michael-betz/espirgbani_pio/src/wifi.c

#include "json_settings.h"
#include "lwip/apps/sntp.h"
#include "lwip/sockets.h"
#include <string.h>
// #include "lwip/sys.h"
#include "esp_event.h"
#include "esp_log.h"
#include "esp_wifi.h"
#include "lwip/dns.h"
#include "lwip/netdb.h"
#include "mdns.h"
#include "nvs_flash.h"
#include "rom/rtc.h"
#include "static_ws.h"
#include "wifi.h"

#include "esp_dpp.h"
#include "qrcode.h"

#define E(x) ESP_ERROR_CHECK_WITHOUT_ABORT(x)

static const char *T = "WIFI";

t_wifi_state wifi_state = WIFI_NOT_CONNECTED;
esp_ip4_addr_t wifi_ip = {0};
char wifi_ssid[32] = {0};

// -----------------------------------------------
//  Websocket logger
// -----------------------------------------------
// Rolling buffer size in RTC mem for log entries in bytes
#define LOG_FILE_SIZE 3576

// put the buffer and write pointer in RTC memory,
// such that it survives sleep mode
RTC_NOINIT_ATTR static char rtcLogBuffer[LOG_FILE_SIZE];
RTC_NOINIT_ATTR static char *rtcLogWritePtr = rtcLogBuffer;
RTC_NOINIT_ATTR static char *rtcLogReadPtr = rtcLogBuffer;

static const char *logBuffEnd = rtcLogBuffer + LOG_FILE_SIZE - 1;

// The unmodified stdout file
FILE *old_stdout = NULL;
FILE *old_stderr = NULL;

// add stdout chars to the RTC log buffer.
static int print_to_ws(void *cookie, const char *data, int size) {
	if (old_stdout != NULL)
		fwrite(data, 1, size, old_stdout);

	// ring-buffer in RTC memory for persistence in sleep mode
	for (unsigned i = 0; i < size; i++) {
		char c = data[i];

		*rtcLogWritePtr = c;
		if (rtcLogWritePtr >= logBuffEnd) {
			rtcLogWritePtr = rtcLogBuffer;
		} else {
			rtcLogWritePtr++;
		}
	}

	return size;
}

void web_console_init() {
	static char linebuf[128];

	ESP_LOGI(T, "Enabling web-socket logging 👋");

	int reason = rtc_get_reset_reason(0);
	if (reason == POWERON_RESET) {
		ESP_LOGW(T, "Clearing RTC log");
		memset(rtcLogBuffer, 0, LOG_FILE_SIZE);
		rtcLogWritePtr = rtcLogBuffer;
		rtcLogReadPtr = rtcLogBuffer;
	} else {
		if (rtcLogWritePtr < rtcLogBuffer || rtcLogWritePtr > logBuffEnd)
			rtcLogWritePtr = rtcLogBuffer;

		if (rtcLogReadPtr < rtcLogBuffer || rtcLogReadPtr > logBuffEnd)
			rtcLogReadPtr = rtcLogBuffer;
	}

	// Keep a copy for printing to UART
	old_stdout = stdout;
	old_stderr = stderr;

	// standard IO streams are inherited when a task is created, so this needs
	// to be done before creating other tasks:
	_GLOBAL_REENT->_stdout = fwopen(NULL, &print_to_ws);
	_GLOBAL_REENT->_stderr = fwopen(NULL, &print_to_ws);

	// Also redirect stdout/stderr of main task
	stdout = _GLOBAL_REENT->_stdout;
	stderr = _GLOBAL_REENT->_stderr;

	setvbuf(stdout, linebuf, _IOLBF, sizeof(linebuf));
}

void wsDumpRtc(httpd_req_t *req, bool dump_all) {
	int n_bytes = 0;

	if (dump_all) {
		n_bytes = LOG_FILE_SIZE;
		rtcLogReadPtr = rtcLogWritePtr;
	} else {
		n_bytes = (rtcLogWritePtr - rtcLogReadPtr + LOG_FILE_SIZE);
		n_bytes %= LOG_FILE_SIZE;
	}

	if (n_bytes <= 0)
		return;

	char *buffer = malloc(n_bytes + 1);
	if (!buffer)
		return;

	char *p = buffer;
	*p++ = 'a';

	for (unsigned i = 0; i < n_bytes; i++) {
		*p++ = *rtcLogReadPtr++;
		if (rtcLogReadPtr > logBuffEnd)
			rtcLogReadPtr = rtcLogBuffer;
	}

	httpd_ws_frame_t wsf = {0};
	wsf.type = HTTPD_WS_TYPE_TEXT;
	wsf.payload = (uint8_t *)buffer;
	wsf.len = n_bytes + 1;
	httpd_ws_send_frame(req, &wsf);

	free(buffer);
}

// go through wifi scan results and look for the first known wifi
// if the wifi is known, meaning it is configured in the .json, connect to it
// if no known wifi is found, start the AP
static void scan_done(
	void *arg, esp_event_base_t event_base, int32_t event_id, void *event_data
) {
	uint16_t n = 24;
	static wifi_ap_record_t ap_info[24];

	E(esp_wifi_scan_get_ap_records(&n, ap_info));

	if (n < 1) {
		ESP_LOGE(T, "wifi scan failed");
		return;
	}

	cJSON *jWifi, *jWifis = jGet(getSettings(), "wifis");
	if (!jWifis) {
		ESP_LOGE(T, "no wifis defined in .json");
		return;
	}

	// Go through all found APs, use ssid as key and try to get item from json
	ESP_LOGI(T, "Wifis I can see:");
	for (unsigned i = 0; i < n; i++) {
		ESP_LOGI(
			T, "    %s (%d, %d dBm)", ap_info[i].ssid, ap_info[i].primary,
			ap_info[i].rssi
		);
	}

	for (unsigned i = 0; i < n; i++) {
		const char *ssid = (const char *)ap_info[i].ssid;
		jWifi = jGet(jWifis, ssid);
		if (!cJSON_IsString(jWifi))
			continue;

		// Found a known good WIFI, connect to it ...
		ESP_LOGI(T, "Looks familiar: %s", ssid);
		char *pw = jWifi->valuestring;
		wifi_config_t cfg;
		memset(&cfg, 0, sizeof(cfg));
		strncpy((char *)cfg.sta.ssid, ssid, 31);
		strncpy(wifi_ssid, ssid, sizeof(wifi_ssid));
		strncpy((char *)cfg.sta.password, pw, 63);
		cfg.sta.scan_method = WIFI_FAST_SCAN;
		cfg.sta.bssid_set = true;
		memcpy(cfg.sta.bssid, ap_info[i].bssid, 6);
		cfg.sta.channel = ap_info[i].primary;
		cfg.sta.pmf_cfg.capable = true;

		E(esp_wifi_set_mode(WIFI_MODE_STA));
		E(esp_wifi_set_config(ESP_IF_WIFI_STA, &cfg));
		E(esp_wifi_connect());
		E(esp_wifi_set_ps(WIFI_PS_MAX_MODEM));
		return;
	}

	ESP_LOGW(T, "no known Wifi found");
	wifi_state = WIFI_NOT_CONNECTED;
}

static void got_ip(
	void *arg, esp_event_base_t event_base, int32_t event_id, void *event_data
) {
	ip_event_got_ip_t *event = (ip_event_got_ip_t *)event_data;
	wifi_ip = event->ip_info.ip;
	ESP_LOGI(T, "Got ip " IPSTR, IP2STR(&event->ip_info.ip));

	// trigger time sync
	sntp_setoperatingmode(SNTP_OPMODE_POLL);
	const char *ntp_str = jGetS(getSettings(), "ntp_host", "pool.ntp.org");
	sntp_setservername(0, ntp_str);
	sntp_init();

	wifi_state = WIFI_CONNECTED;
}

static void got_discon(
	void *arg, esp_event_base_t event_base, int32_t event_id, void *event_data
) {
	ESP_LOGW(T, "got disconnected :(");
	if (event_data) {
		wifi_event_sta_disconnected_t *ed =
			(wifi_event_sta_disconnected_t *)event_data;
		ESP_LOGW(T, "reason: %d", ed->reason);
	}

	sntp_stop();
	wifi_state = WIFI_NOT_CONNECTED;
}

static void dpp_enrollee_event_cb(esp_supp_dpp_event_t event, void *data) {
	static int retries = 8;

	switch (event) {
	case ESP_SUPP_DPP_URI_READY:
		retries = 8;
		if (data != NULL) {
			esp_qrcode_config_t cfg = ESP_QRCODE_CONFIG_DEFAULT();
			ESP_LOGI(T, "Scan below QR Code to configure the enrollee:\n");
			esp_qrcode_generate(&cfg, (const char *)data);
		}
		break;

	case ESP_SUPP_DPP_CFG_RECVD:
		retries = 8;
		wifi_config_t s_dpp_wifi_config;
		memcpy(&s_dpp_wifi_config, data, sizeof(s_dpp_wifi_config));
		ESP_LOGI(
			T, "DPP Authentication successful, ssid: %s",
			s_dpp_wifi_config.sta.ssid
		);
		// TODO store ssid and pw in .json config, then call tryJsonConnect()
		break;

	case ESP_SUPP_DPP_FAIL:
		ESP_LOGW(T, "DPP Auth failed (Reason: %s)", esp_err_to_name((int)data));
		if (retries-- > 0) {
			ESP_LOGI(T, "retry ...");
			E(esp_supp_dpp_start_listen());
		}
		break;

	default:
		break;
	}
}

static wifi_config_t wifi_ap_config = {
	.ap =
		{
			.channel = 6,
			.max_connection = 3,
			.authmode = WIFI_AUTH_OPEN,
			.pmf_cfg =
				{
					.required = false,
				},
		},
};

void initWifi() {
	// Initialize NVS
	esp_err_t ret = nvs_flash_init();
	if (ret == ESP_ERR_NVS_NO_FREE_PAGES ||
		ret == ESP_ERR_NVS_NEW_VERSION_FOUND) {
		E(nvs_flash_erase());
		ret = nvs_flash_init();
	}
	E(ret);

	E(esp_netif_init());
	E(esp_event_loop_create_default());

	// register some async callbacks
	E(esp_event_handler_register(
		WIFI_EVENT, WIFI_EVENT_SCAN_DONE, &scan_done, NULL
	));
	E(esp_event_handler_register(IP_EVENT, IP_EVENT_STA_GOT_IP, &got_ip, NULL));
	E(esp_event_handler_register(
		WIFI_EVENT, WIFI_EVENT_STA_DISCONNECTED, &got_discon, NULL
	));
	E(esp_event_handler_register(
		WIFI_EVENT, WIFI_EVENT_STA_STOP, &got_discon, NULL
	));

	wifi_init_config_t cfg = WIFI_INIT_CONFIG_DEFAULT();
	E(esp_wifi_init(&cfg));

	// Initialize default station as network interface instance (esp-netif)
	esp_netif_t *sta_netif = esp_netif_create_default_wifi_sta();
	assert(sta_netif);
	esp_netif_t *ap_netif = esp_netif_create_default_wifi_ap();
	assert(ap_netif);

	// Init DNS and mDNS
	const char *hostname = jGetS(getSettings(), "hostname", "espirgbani");
	E(esp_netif_set_hostname(sta_netif, hostname));
	E(mdns_init());
	E(mdns_hostname_set(hostname));

	// Set the timezone
	const char *tz_str = jGetS(getSettings(), "timezone", "PST8PDT");
	ESP_LOGI(T, "Setting timezone to TZ = %s", tz_str);
	setenv("TZ", tz_str, 1);
	tzset();

	// Setup AP mode (may be used if no known wifi is found)
	int l = strlen(hostname);
	if (l > sizeof(wifi_ap_config.ap.ssid))
		l = sizeof(wifi_ap_config.ap.ssid);
	wifi_ap_config.ap.ssid_len = l;
	memcpy(wifi_ap_config.ap.ssid, hostname, l);

	E(esp_wifi_set_mode(WIFI_MODE_STA));
	E(esp_wifi_start());
}

void tryJsonConnect() {
	// Disable wifi if there are no entries in settings.json
	cJSON *jWifis = jGet(getSettings(), "wifis");
	if (!jWifis || cJSON_GetArraySize(jWifis) <= 0) {
		ESP_LOGW(T, "No wifis defined in .json. Disabling wifi.");
		wifi_state = WIFI_DISABLED;
		return;
	}

	// Initialize and start WiFi scan
	E(esp_wifi_set_mode(WIFI_MODE_STA));
	E(esp_wifi_scan_start(NULL, false));
	// fires SYSTEM_EVENT_SCAN_DONE when done, calls scan_done() ...
	wifi_state = WIFI_SCANNING;
}

void tryApMode() {
	E(esp_wifi_set_mode(WIFI_MODE_AP));
	E(esp_wifi_set_config(WIFI_IF_AP, &wifi_ap_config));
	ESP_LOGI(T, "started AP mode. SSID: %s", wifi_ap_config.ap.ssid);
	strncpy(wifi_ssid, (const char *)wifi_ap_config.ap.ssid, sizeof(wifi_ssid));
	wifi_state = WIFI_AP_MODE;
}

void tryEasyConnect() {
	// nice idea but doesn't work
	E(esp_wifi_set_mode(WIFI_MODE_STA));
	E(esp_supp_dpp_init(dpp_enrollee_event_cb));
	E(esp_supp_dpp_bootstrap_gen(
		"6", // DPP Bootstrapping listen channels separated by commas.
		DPP_BOOTSTRAP_QR_CODE,
		NULL, // Private key string for DPP Bootstrapping in PEM format.
		NULL  // Additional ancillary information to be included in QR Code.
	));

	E(esp_supp_dpp_start_listen());
	ESP_LOGI(T, "Started listening for DPP Authentication");
	wifi_state = WIFI_DPP_LISTENING;
}
