michael-betz/espirgbani_pio/src/shaders.c

// The animated background patterns

#include <frame_buffer.h>
#include "shaders.h"
#include "fast_hsv2rgb.h"
#include "palette.h"
#include <math.h>
#include <stdio.h>
#include <stdbool.h>
#include <stdlib.h>
#include <time.h>
#include "esp_log.h"

#if defined(ESP_PLATFORM)
#include "esp_timer.h"
#include "freertos/FreeRTOS.h"
#include "freertos/task.h"
#include "json_settings.h"
#include "rgb_led_panel.h"
#endif

static const char *T = "SHADERS";

void drawXorFrame(unsigned frm) {
	static uint16_t aniZoom = 0x04, boost = 7;
	for (int y = 0; y <= 31; y++)
		for (int x = 0; x <= 127; x++)
			setPixel(
				0, x, y,
				SRGBA(
					((x + y + frm) & aniZoom) * boost,
					((x - y - frm) & aniZoom) * boost,
					((x ^ y) & aniZoom) * boost, 0xFF
				)
			);
	if ((frm % 1024) == 0) {
		aniZoom = rand();
		boost = RAND_AB(1, 8);
	}
}

void drawBendyFrame(unsigned frm) {
	static int i = 2, j = 3, k = ((2 << 5) - 1), l = ((3 << 5) - 1);
	int temp1, temp2, f = frm % 3000;
	if (f == 0) {
		i = RAND_AB(1, 8);
		j = RAND_AB(1, 8);
		k = ((i << 5) - 1);
		l = ((j << 5) - 1);
	}
	for (int y = 0; y <= 31; y++) {
		for (int x = 0; x <= 127; x++) {
			temp1 = abs(((i * y + (f * 16) / (x + 16)) % 64) - 32) * 7;
			temp2 = abs(((j * x + (f * 16) / (y + 16)) % 64) - 32) * 7;
			setPixel(
				0, x, y,
				SRGBA(temp1 & k, temp2 & l, (temp1 ^ temp2) & 0x88, 0xFF)
			);
		}
	}
}

void drawAlienFlameFrame(unsigned frm) {
	//  *p points to last pixel of second last row (lower right)
	// uint32_t *p =
	// (uint32_t*)g_frameBuff[0][DISPLAY_WIDTH*(DISPLAY_HEIGHT-1)-1]; uint32_t
	// *tempP;
	uint32_t colIndex, temp;
	colIndex = RAND_AB(0, 127);
	temp = getPixel(0, colIndex, 31);
	setPixel(0, colIndex, 31, 0xFF000000 | (temp + 2));
	colIndex = RAND_AB(0, 127);
	temp = getPixel(0, colIndex, 31);
	temp = scale32(127, temp);
	setPixel(0, colIndex, 31, temp);
	for (int y = 30; y >= 0; y--) {
		for (int x = 0; x <= 127; x++) {
			colIndex = RAND_AB(0, 2);
			temp = GC(getPixel(0, x - 1, y + 1), colIndex);
			temp += GC(getPixel(0, x, y + 1), colIndex);
			temp += GC(getPixel(0, x + 1, y + 1), colIndex);
			setPixelColor(0, x, y, RAND_AB(0, 2), MIN(temp * 5 / 8, 255));
		}
	}
}

// We add 1 extra row for seeding the flames
static uint8_t pbuff[DISPLAY_WIDTH * (DISPLAY_HEIGHT + 1)];

static void flameSeedRow() {
	int c = 0, v = 0;
	uint8_t *p = &pbuff[DISPLAY_HEIGHT * DISPLAY_WIDTH];
	// ESP_LOGI(T, "flameseed");
	for (unsigned x = 0; x < DISPLAY_WIDTH; x++) {
		if (c <= 0) {
			c = RAND_AB(0, 5);	   // block width
			v = RAND_AB(-1, 1); // intensity
		}
		*p += v;
		// Detect negative underflow
		if (*p > 128)
			*p = 0;
		// Detect positive overflow
		else if (*p >= P_SIZE)
			*p = P_SIZE - 1;
		p++;
		c -= 1;
	}
}

static void flameSpread(int x, int y, bool randomize) {
	static int wind = 1, heat_damper = 4;

	if (randomize) {
		wind = RAND_AB(-2, 1);
		heat_damper = RAND_AB(4, 10);
		ESP_LOGI(T, "flameSpread() wind = %d, damp = %d", wind, heat_damper);
		return;
	}

	// source index
	int ind = x + y * DISPLAY_WIDTH;

	// random horizontal location offset to simulate wind
	int x_ = (x + wind + RAND_AB(0, 1) + DISPLAY_WIDTH) % DISPLAY_WIDTH;

	// target index
	int ind_ = x_ + (y - 1) * DISPLAY_WIDTH;

	// propagate the pixel to the row above with dampening
	uint8_t pixel = pbuff[ind];
	uint8_t pixel_ = pbuff[ind_];

	int heat = pixel - RAND_AB(0, heat_damper);  // the max can be 2, 3, 4, 5
	if (heat <= 0) {
		pbuff[ind_] = 0;
		return;
	}

	if (heat_damper >= 7)
		heat += pixel_ / 4;
	else
		heat += pixel_ / 8;

	if (heat >= P_SIZE)
		heat = P_SIZE - 1;

	pbuff[ind_] = heat;
}

void drawDoomFlameFrame(unsigned frm) {
	static const unsigned *pal = NULL;
	if (pal == NULL)
		pal = get_palette(0);

	// Slowly modulate flames / change palette now and then
	if ((frm % 25) == 0) {
		flameSeedRow();
		if ((frm % 15000) == 0) {
			pal = get_random_palette();
			flameSpread(0, 0, true);
		}
	}

	// Flame generation
	for (int y = DISPLAY_HEIGHT; y > 0; y--)
		for (int x = 0; x < DISPLAY_WIDTH; x++)
			flameSpread(x, y, false);

	// Colorize flames and write into framebuffer
	for (unsigned y = 0; y < DISPLAY_HEIGHT; y++) {
		for (unsigned x = 0; x < DISPLAY_WIDTH; x++) {
			uint8_t pInd = pbuff[x + y * DISPLAY_WIDTH];
			setPixel(0, x, y, pal[pInd % P_SIZE]);
		}
	}
}

void drawLasers(unsigned frm) {
	// aaLine: ~1 ms   aaLine2: ~4 ms
	static float alpha = 0.0, ri = 10;
	static unsigned n_lines = 8, x = 64, y = 16;
	static bool do_clear = true;
	unsigned shades[N_SHADES];

	if (frm % 2000 == 0) {
		n_lines = RAND_AB(3, 32);		   // number of lines
		x = RAND_AB(4, DISPLAY_WIDTH - 5); // center point
		y = RAND_AB(1, DISPLAY_HEIGHT - 2);
		ri = RAND_AB(0, 200) / 10.0; // inner radius
		do_clear = RAND_AB(0, 1);

		// Prevent this float from getting too big and loosing precision eventually
		while (alpha > M_PI * 8)
			alpha -= M_PI * 8;
	}

	if (do_clear)
		setAll(0, 0xFF000000);

	for (unsigned i = 0; i < n_lines; i++) {
		float dx = cos(alpha + M_PI * 2 * i / n_lines);
		float dy = sin(alpha + M_PI * 2 * i / n_lines);

		set_shade_ht(HSV_HUE_MAX * i / n_lines, shades);
		aaLine2(
			0, shades, x + dx * ri, y + dy * ri, x + dx * DISPLAY_WIDTH,
			y + dy * DISPLAY_WIDTH
		);
	}

	alpha += 0.002;
}

#if defined(ESP_PLATFORM)
void aniBackgroundTask(void *pvParameters) {
	unsigned frm = 1, aniMode = 0;
	unsigned _f_del = g_f_del / portTICK_PERIOD_MS;

	setAll(0, 0xFF000000);

	// delay between selecting a new random background shader
	// set to <= 0 to disable background shaders
	cJSON *jDelay = jGet(getSettings(), "delays");
	int shader_delay = jGetI(jDelay, "shader", 300); // [s]
	shader_delay = shader_delay * 1000 / _f_del;	 // [cycles]
	ESP_LOGI(T, "started aniBackgroundTask(), shader_delay: %d", shader_delay);

	TickType_t xLastWakeTime = xTaskGetTickCount();
	while (1) {
		uint64_t t = esp_timer_get_time();

		if ((shader_delay > 0) && (frm % shader_delay == 0)) {
			aniMode = RAND_AB(0, 8); // choose black screen more often
			if (aniMode == 0 || aniMode > 5)
				setAll(0, 0xFF000000);
		}

		switch (aniMode) {
		case 1:
			// cool square patterns
			drawXorFrame(frm);
			break;

		case 2:
			// slowly bending zebra curves
			drawBendyFrame(frm);
			break;

		case 3:
			// RGB pixelated smoke
			drawAlienFlameFrame(frm);
			break;

		case 4:
			// doom fire with different palettes
			drawDoomFlameFrame(frm);
			break;

		case 5:
			// radial lasers
			drawLasers(frm);
			break;
		}

		unsigned dt = esp_timer_get_time() - t;
		if (aniMode <= 5 && frm % 1000 == 0)
			ESP_LOGI(T, "shader: %d, dt = %d us, frm = %d", aniMode, dt, frm);

		// maximum global frame-rate: 1 / f_del kHz
		vTaskDelayUntil(&xLastWakeTime, _f_del);
		updateFrame();
		frm++;
	}
}
#endif
