michael-betz/espirgbani_pio/src/wifi.h

#ifndef WIFI_H
#define WIFI_H

#include "esp_http_server.h"
#include "esp_wifi.h"

typedef enum {
	WIFI_DISABLED,
	WIFI_NOT_CONNECTED,
	WIFI_SCANNING,
	WIFI_DPP_LISTENING,
	WIFI_CONNECTED,
	WIFI_AP_MODE,
} t_wifi_state;

extern t_wifi_state wifi_state;
extern esp_ip4_addr_t wifi_ip;
extern char wifi_ssid[32];

// -------------------
//  wifi connection
// -------------------
void initWifi();

void tryJsonConnect();
void tryApMode();
void tryEasyConnect();

// -------------------
//  websocket logging
// -------------------
void web_console_init();

// dump the whole RTC buffer to the WS, oldest entries first.
// call this once the WS connection is open.
void wsDumpRtc(httpd_req_t *req, bool dump_all);

#endif
