michael-betz/espirgbani_pio/src/animations.h

#ifndef ANIMATIONS_H
#define ANIMATIONS_H

#include <stdio.h>

#define HEADER_OFFS 0x0000C800
#define HEADER_SIZE 0x00000200

#define SWAP16(x) ((x >> 8) | (x << 8))
#define SWAP32(x)                                                              \
	(((x >> 24) & 0xff) | ((x << 8) & 0xff0000) | ((x >> 8) & 0xff00) |        \
	 ((x << 24) & 0xff000000))

typedef struct {
	uint16_t nAnimations;
	char buildStr[9];
} fileHeader_t;

// Type of the frame header table
typedef struct {
	uint8_t frameId;  // 1-based frame index
	uint8_t frameDur; // Frame duration [ms]
} frameHeaderEntry_t;

typedef struct {
	uint16_t animationId;
	uint8_t unknown0; // almost always 1
	uint8_t nStoredFrames;
	uint32_t byteOffset;   // points to frameTable
	uint8_t nFrameEntries; // in the frame table
	uint8_t width;		   //[pixels]
	uint8_t height;		   //[pixels]
	uint8_t unknown1[9];
	char name[32];					 // zero terminated
	frameHeaderEntry_t *frameHeader; // the frame table
} __attribute__((__packed__)) headerEntry_t;

// blocks and forever shows pinball animations on layer 2
void aniPinballTask(void *pvParameters);

#endif
