michael-betz/espirgbani_pio/src/val2pwm.c

// Copyright 2017 Espressif Systems (Shanghai) PTE LTD
//
// Licensed under the Apache License, Version 2.0 (the "License");
// you may not use this file except in compliance with the License.
// You may obtain a copy of the License at
//
//     http://www.apache.org/licenses/LICENSE-2.0
//
// Unless required by applicable law or agreed to in writing, software
// distributed under the License is distributed on an "AS IS" BASIS,
// WITHOUT WARRANTIES OR CONDITIONS OF ANY KIND, either express or implied.
// See the License for the specific language governing permissions and
// limitations under the License.

#include "val2pwm.h"
#include <stdint.h>

// C/p'ed from
// https://ledshield.wordpress.com/2012/11/13/led-brightness-to-your-eye-gamma-correction-no/
const uint16_t lumConvTab[] = {
	65535, 65508, 65479, 65451, 65422, 65394, 65365, 65337, 65308, 65280, 65251,
	65223, 65195, 65166, 65138, 65109, 65081, 65052, 65024, 64995, 64967, 64938,
	64909, 64878, 64847, 64815, 64781, 64747, 64711, 64675, 64637, 64599, 64559,
	64518, 64476, 64433, 64389, 64344, 64297, 64249, 64200, 64150, 64099, 64046,
	63992, 63937, 63880, 63822, 63763, 63702, 63640, 63577, 63512, 63446, 63379,
	63310, 63239, 63167, 63094, 63019, 62943, 62865, 62785, 62704, 62621, 62537,
	62451, 62364, 62275, 62184, 62092, 61998, 61902, 61804, 61705, 61604, 61501,
	61397, 61290, 61182, 61072, 60961, 60847, 60732, 60614, 60495, 60374, 60251,
	60126, 59999, 59870, 59739, 59606, 59471, 59334, 59195, 59053, 58910, 58765,
	58618, 58468, 58316, 58163, 58007, 57848, 57688, 57525, 57361, 57194, 57024,
	56853, 56679, 56503, 56324, 56143, 55960, 55774, 55586, 55396, 55203, 55008,
	54810, 54610, 54408, 54203, 53995, 53785, 53572, 53357, 53140, 52919, 52696,
	52471, 52243, 52012, 51778, 51542, 51304, 51062, 50818, 50571, 50321, 50069,
	49813, 49555, 49295, 49031, 48764, 48495, 48223, 47948, 47670, 47389, 47105,
	46818, 46529, 46236, 45940, 45641, 45340, 45035, 44727, 44416, 44102, 43785,
	43465, 43142, 42815, 42486, 42153, 41817, 41478, 41135, 40790, 40441, 40089,
	39733, 39375, 39013, 38647, 38279, 37907, 37531, 37153, 36770, 36385, 35996,
	35603, 35207, 34808, 34405, 33999, 33589, 33175, 32758, 32338, 31913, 31486,
	31054, 30619, 30181, 29738, 29292, 28843, 28389, 27932, 27471, 27007, 26539,
	26066, 25590, 25111, 24627, 24140, 23649, 23153, 22654, 22152, 21645, 21134,
	20619, 20101, 19578, 19051, 18521, 17986, 17447, 16905, 16358, 15807, 15252,
	14693, 14129, 13562, 12990, 12415, 11835, 11251, 10662, 10070, 9473,  8872,
	8266,  7657,  7043,	 6424,	5802,  5175,  4543,	 3908,	3267,  2623,  1974,
	1320,  662,	  0};

uint8_t valToPwm(int val) {
	if (val < 0)
		val = 0;
	if (val > 255)
		val = 255;
	return (65535 - lumConvTab[val]) >> 8;
}
